Mosiah-Beal/411-Practicum/Planning Documents/Level1_Diagram.drawio.png

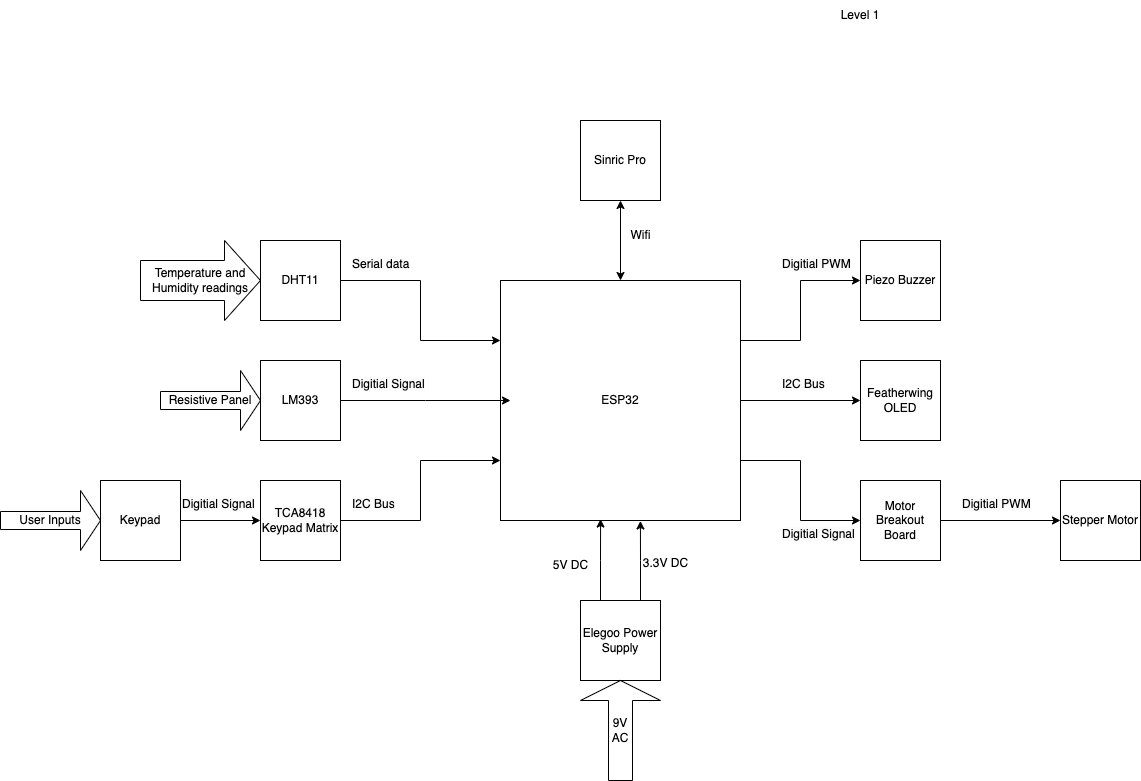
Planning Documents/Level1_Diagram.drawio.png
