Mosiah-Beal/411-Practicum/PNG's and PDF's/Planning Diagrams/411 Practicum Project Planning.drawio.pdf

# MAIN PR Undec

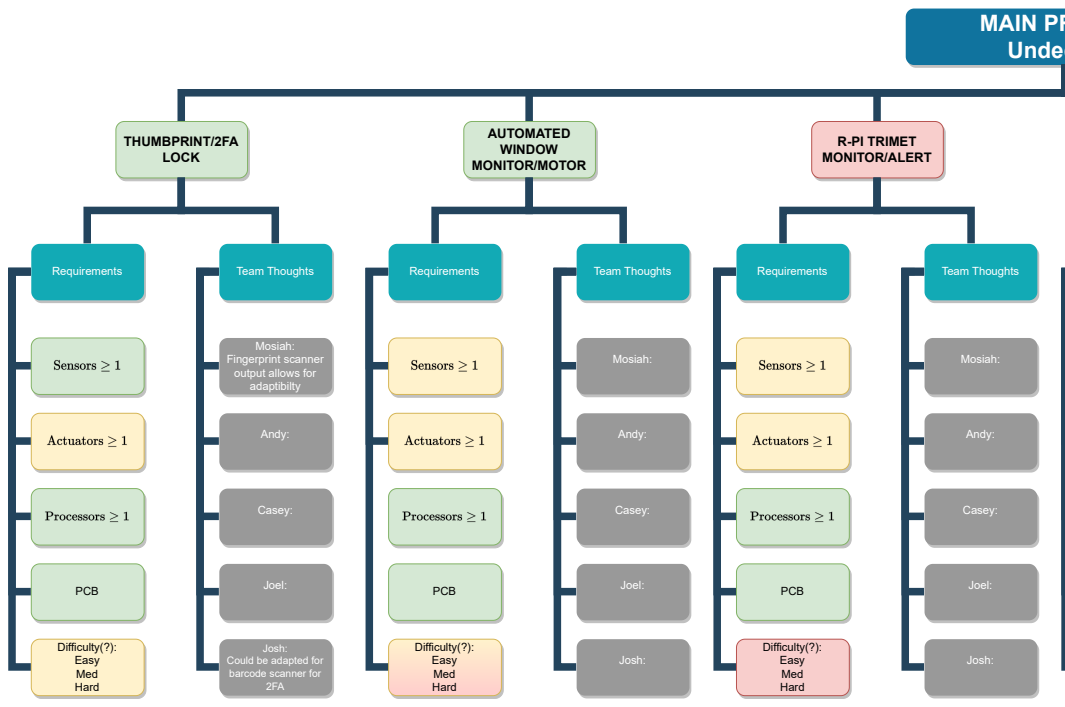
[picture p22: page 1]
THUMBPRINT/2FA LOCK; AUTOMATED WINDOW MONITOR/MOTOR; R-PI TRIMET MONITOR/ALERT; Requirements; Team Thoughts; PCB; Difficulty(?): Easy Med Hard; Andy:; Casey:; Joel:; Josh:; Difficulty(?): Easy Med; Mosiah:

Mosiah:
Fingerprint scanner
output allows for
adaptibilty

Could be adapted for
barcode scanner for

# ROJECT cided

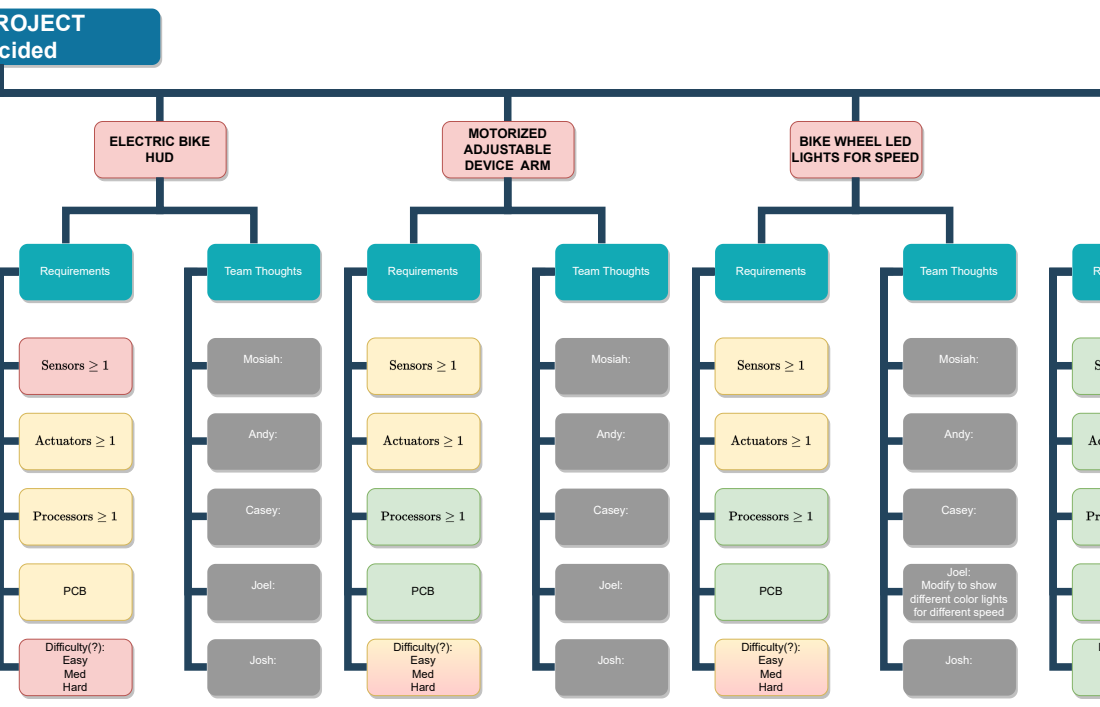
[picture p23: page 2]
ELECTRIC BIKE HUD; MOTORIZED ADJUSTABLE DEVICE ARM; Requirements; Team Thoughts; PCB; Difficulty(?): Easy Med; Mosiah:; Andy:; Casey:; Joel:; Josh:

BIKE WHEEL LED
LIGHTS FOR SPEED

Joel:
Modify to show
different color lights
for different speed

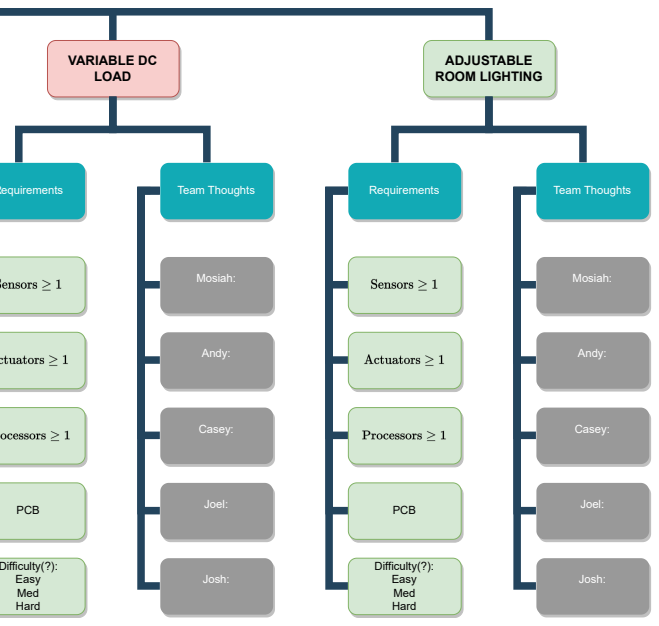
[picture p24: page 3]
VARIABLE DC LOAD; Requirements; Team Thoughts; PCB; Difficulty(?): Easy Med; Mosiah:; Andy:; Casey:; Joel:; Josh:; ADJUSTABLE ROOM LIGHTING
