Mosiah-Beal/411-Practicum/PNG's and PDF's/Schematics and PCBs/Archive/Window_Weather_Monitor-SCH_PCB_rev4.pdf

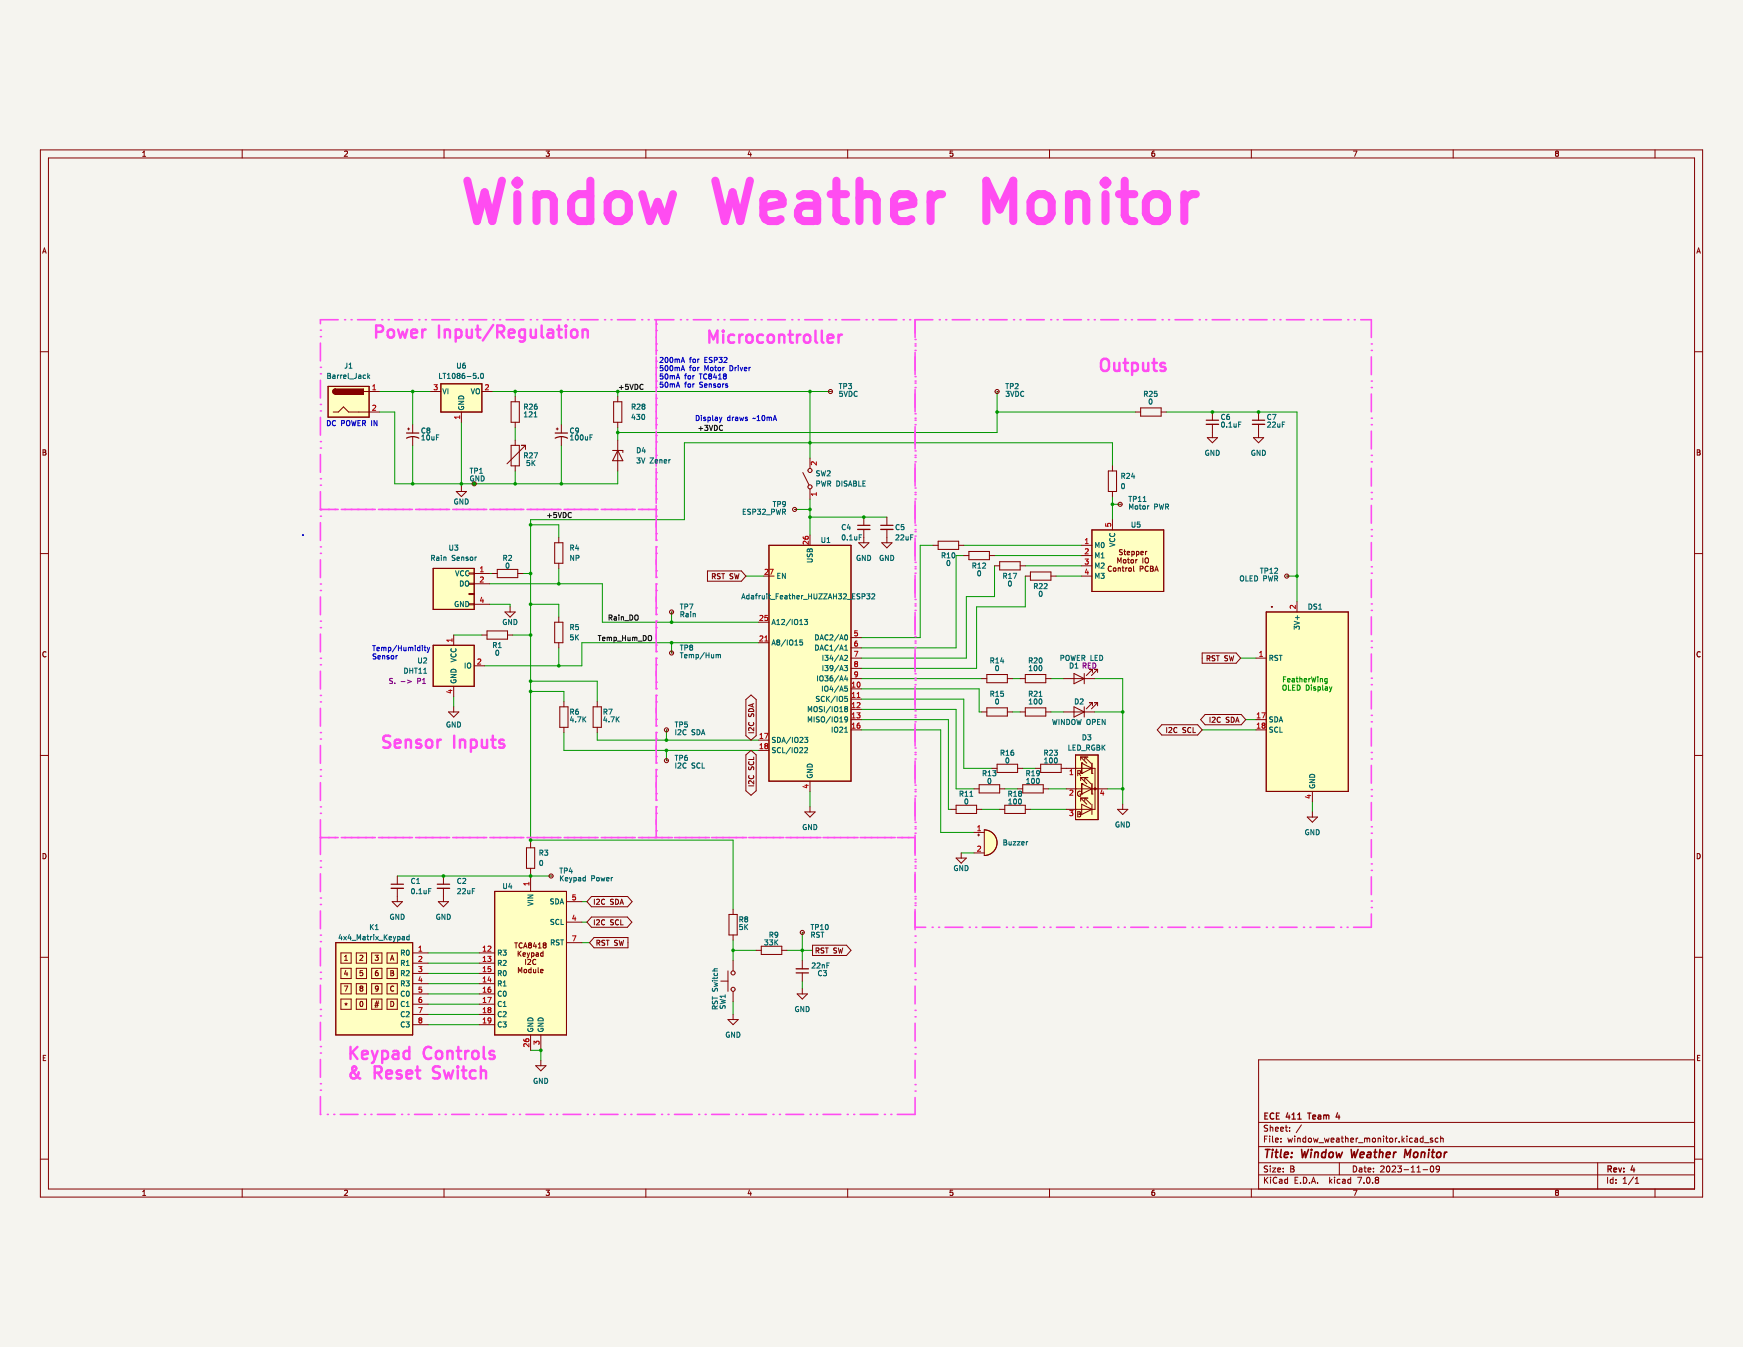
[picture p32: page 1]

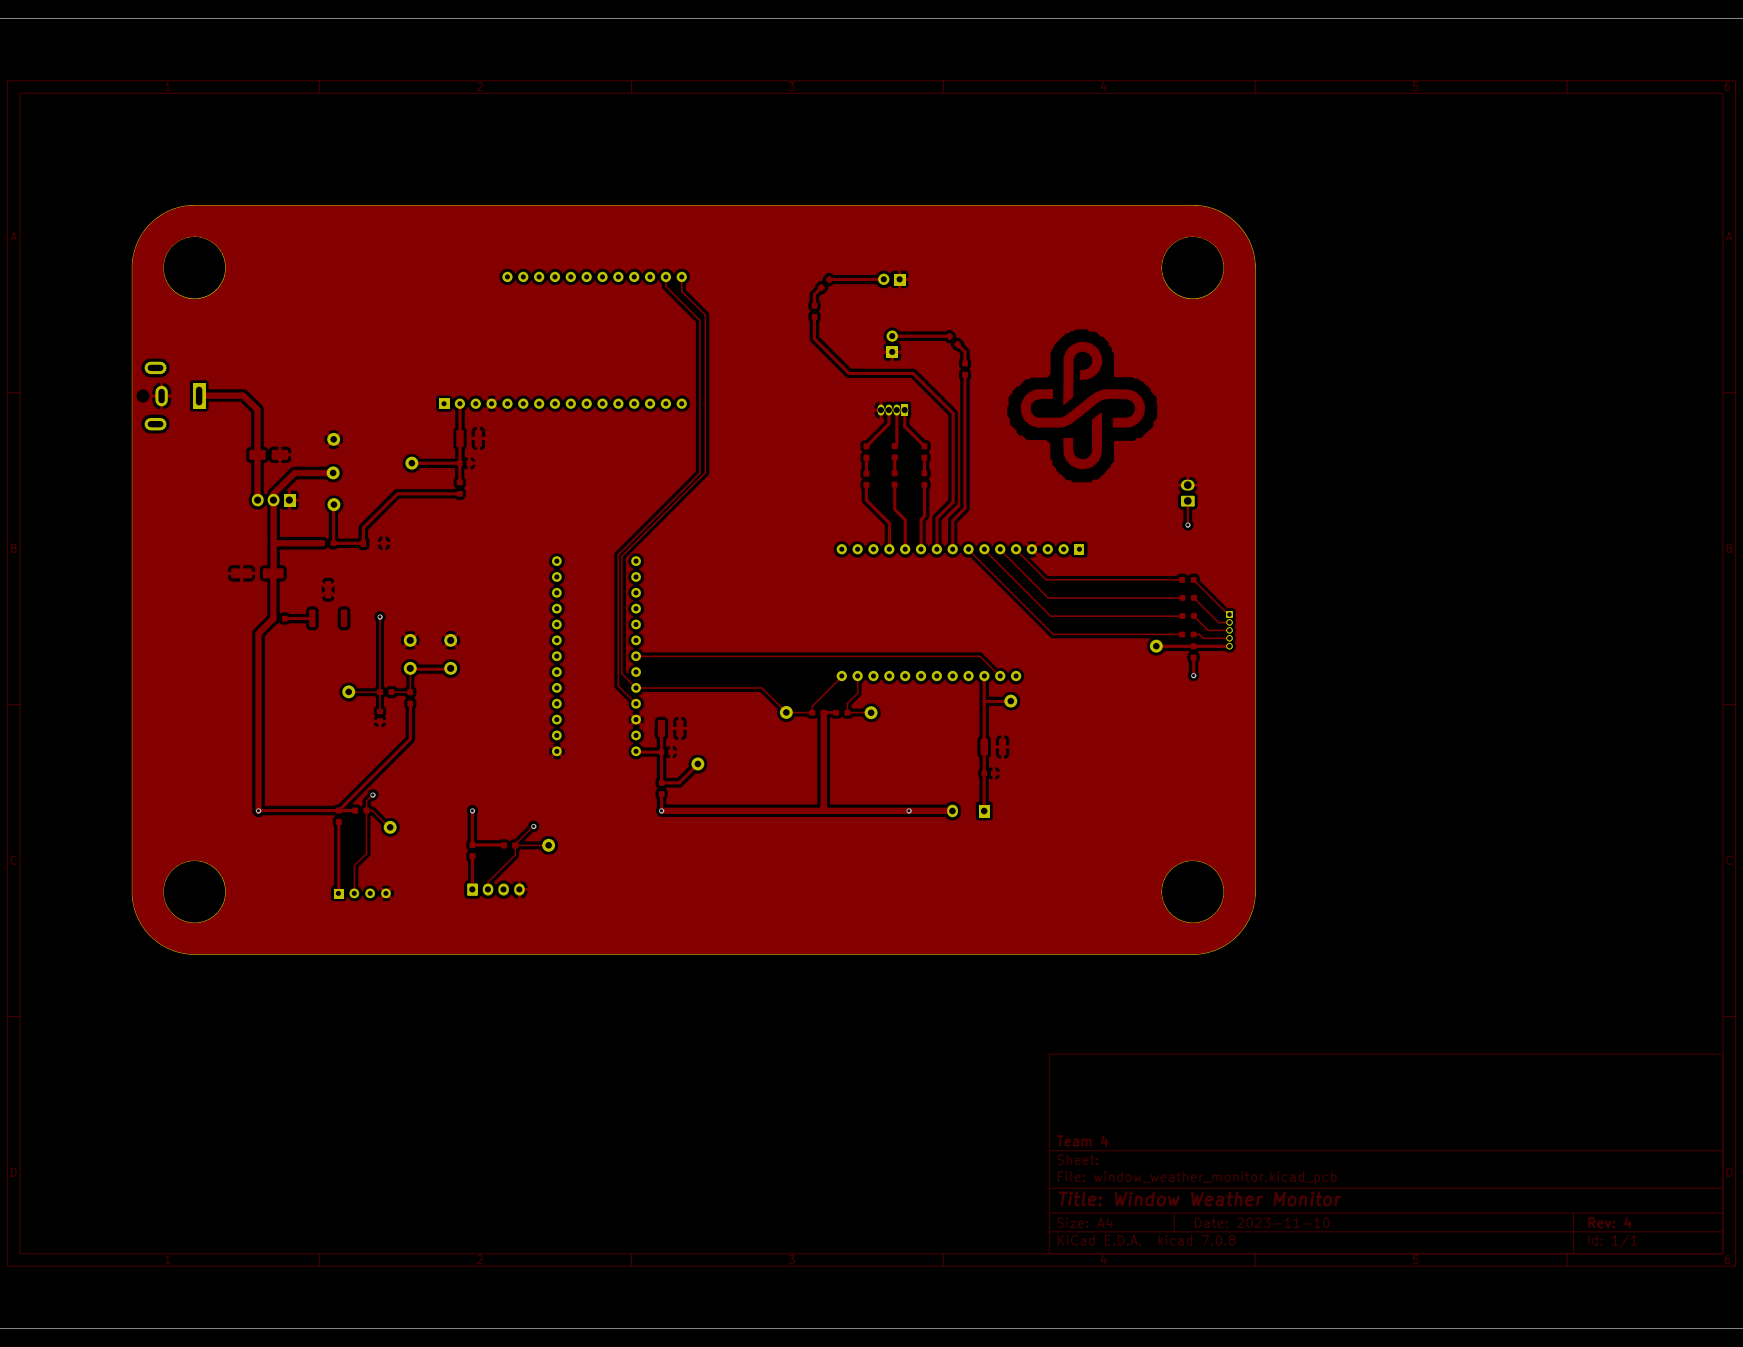
[picture p33: page 2]

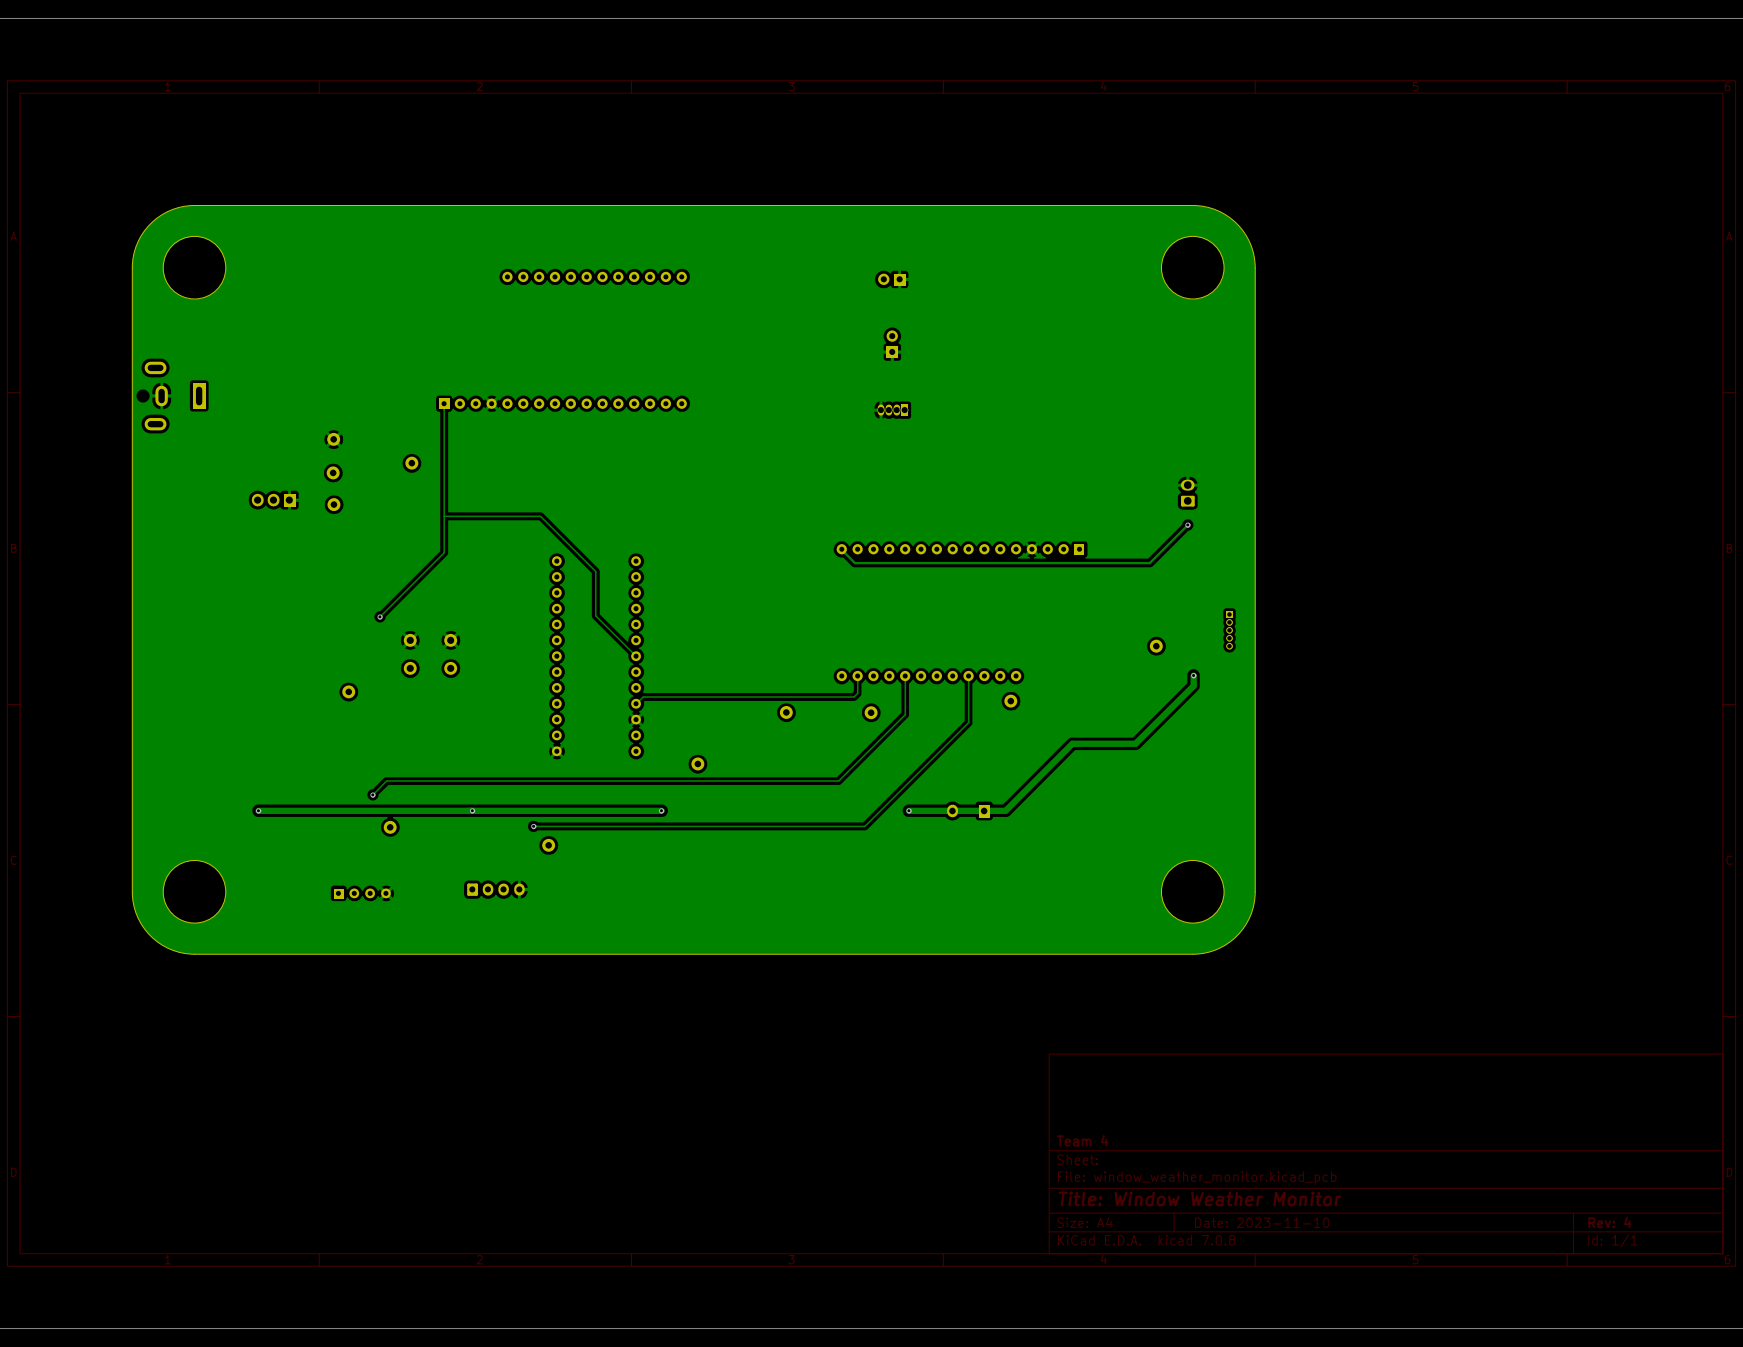
[picture p34: page 3]


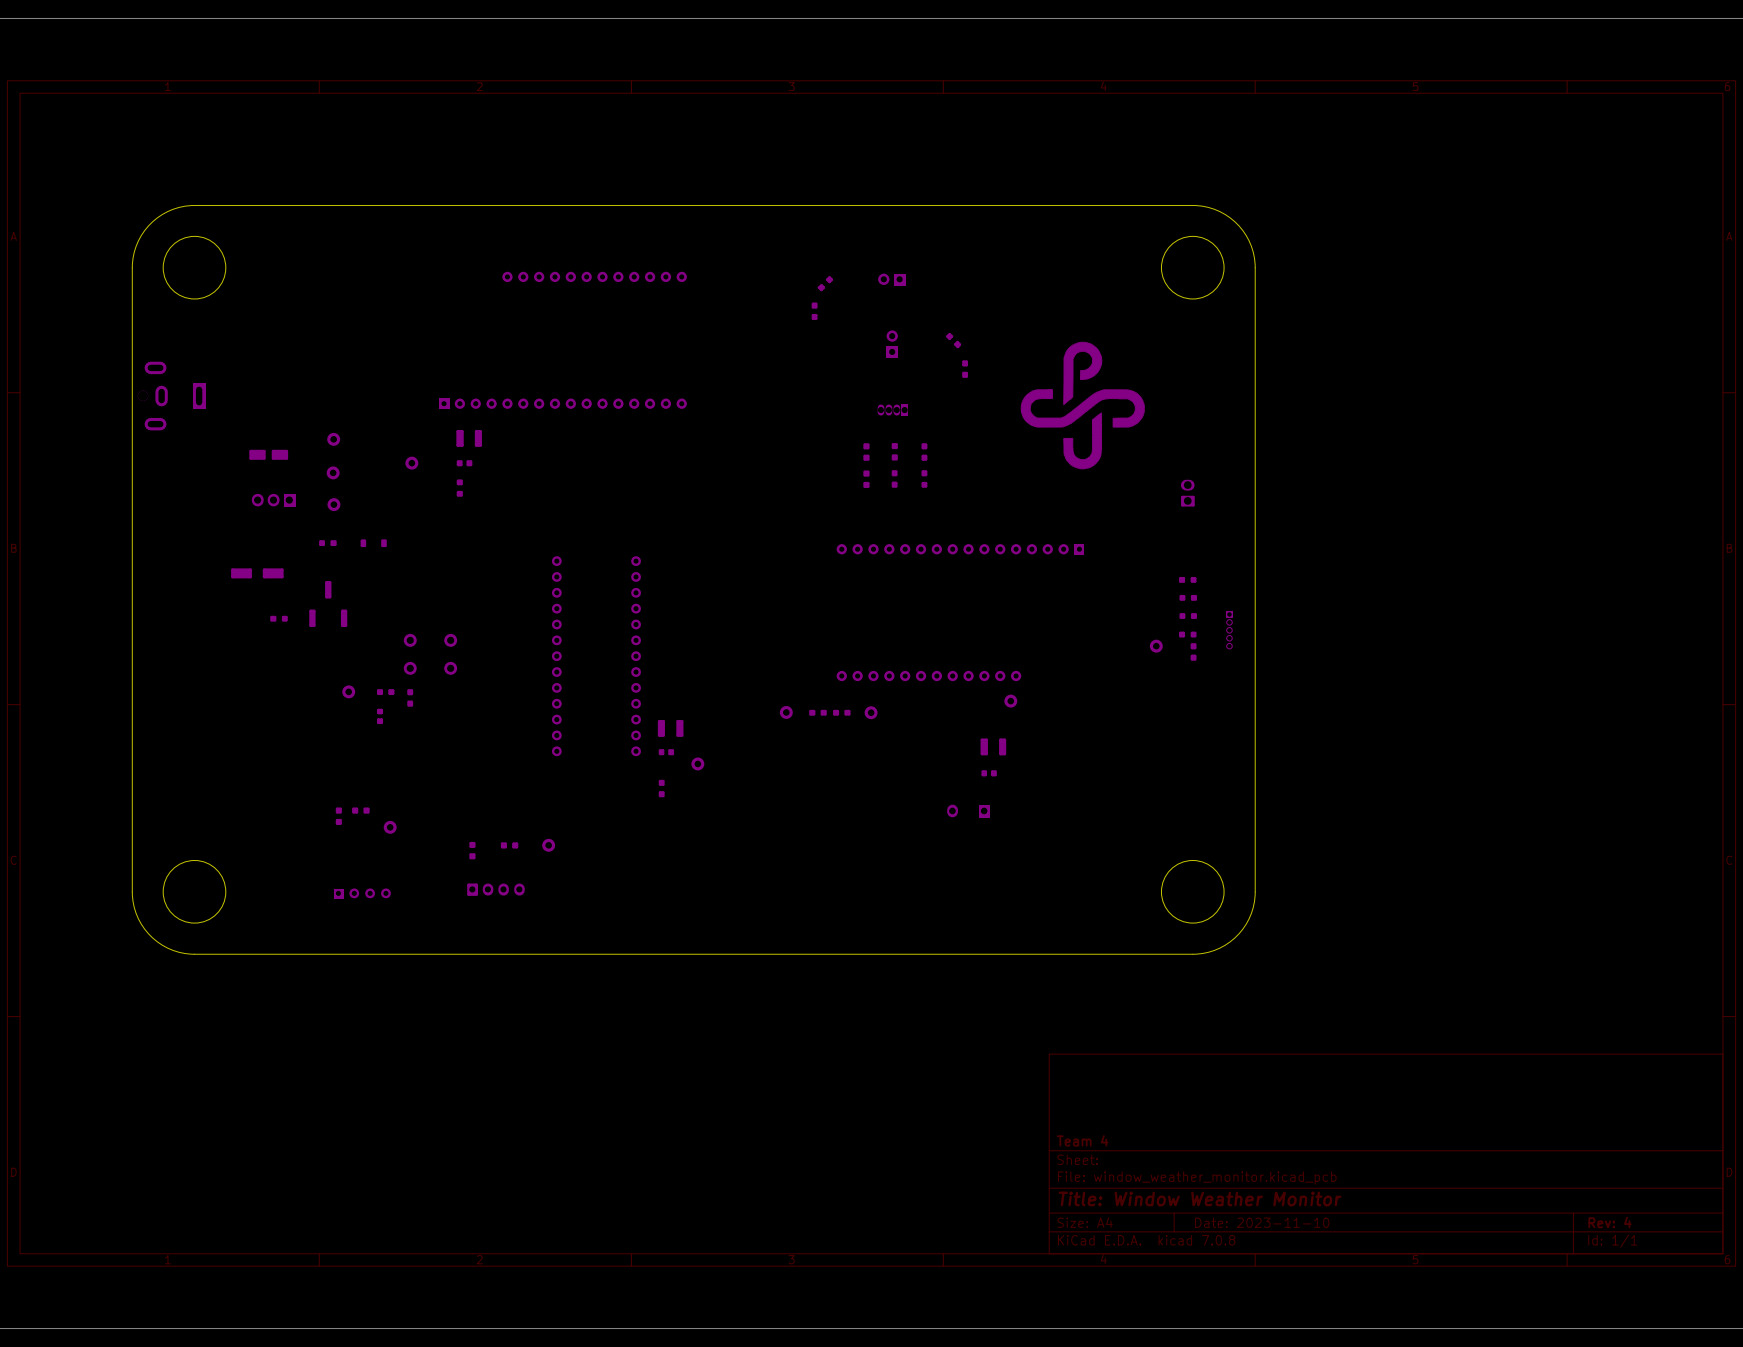
[picture p35: page 5]
