Mosiah-Beal/411-Practicum/PNG's and PDF's/Schematics and PCBs/Archive/Window_Weather_Monitor-PCB_rev3.pdf

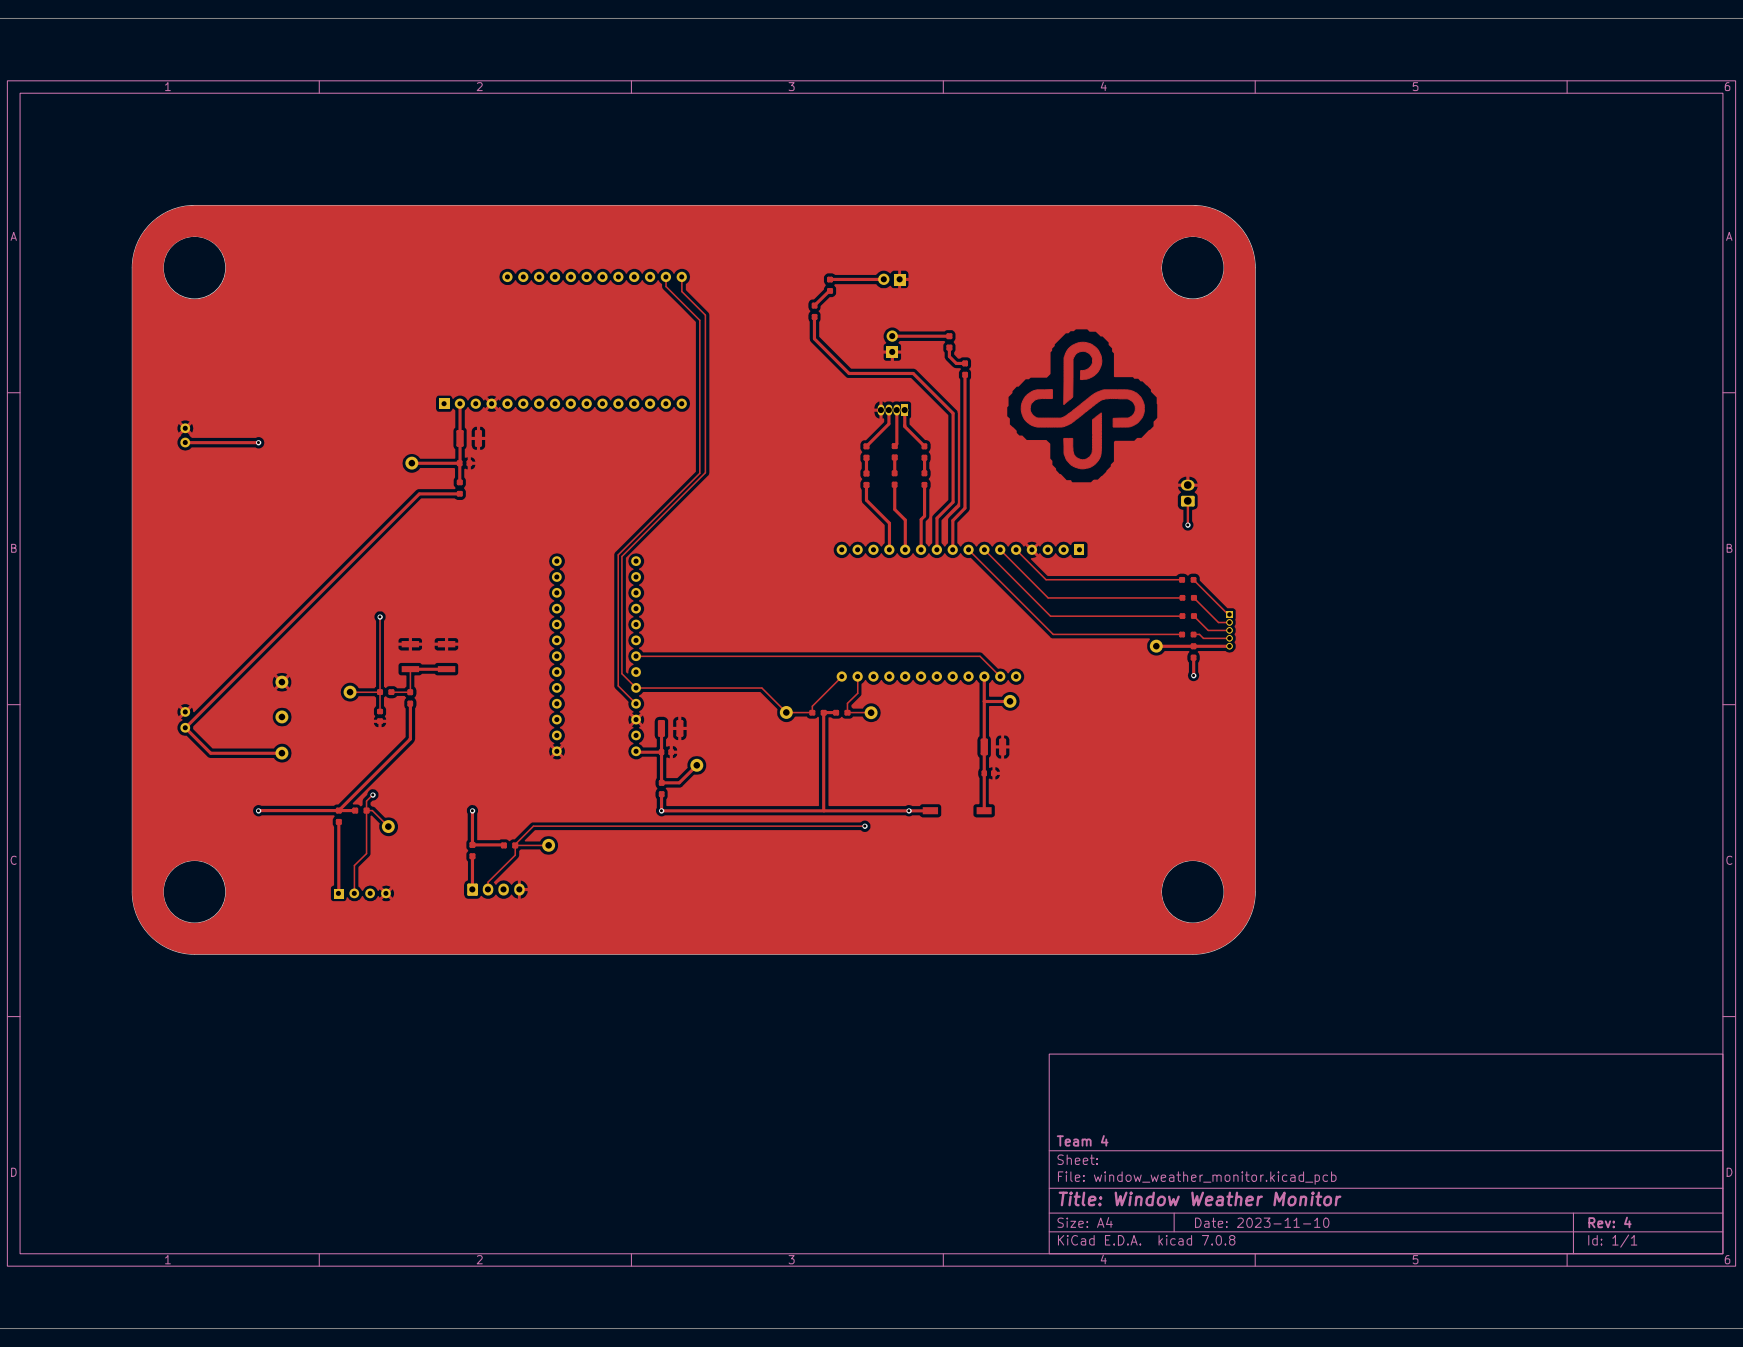
[picture p36: page 1]

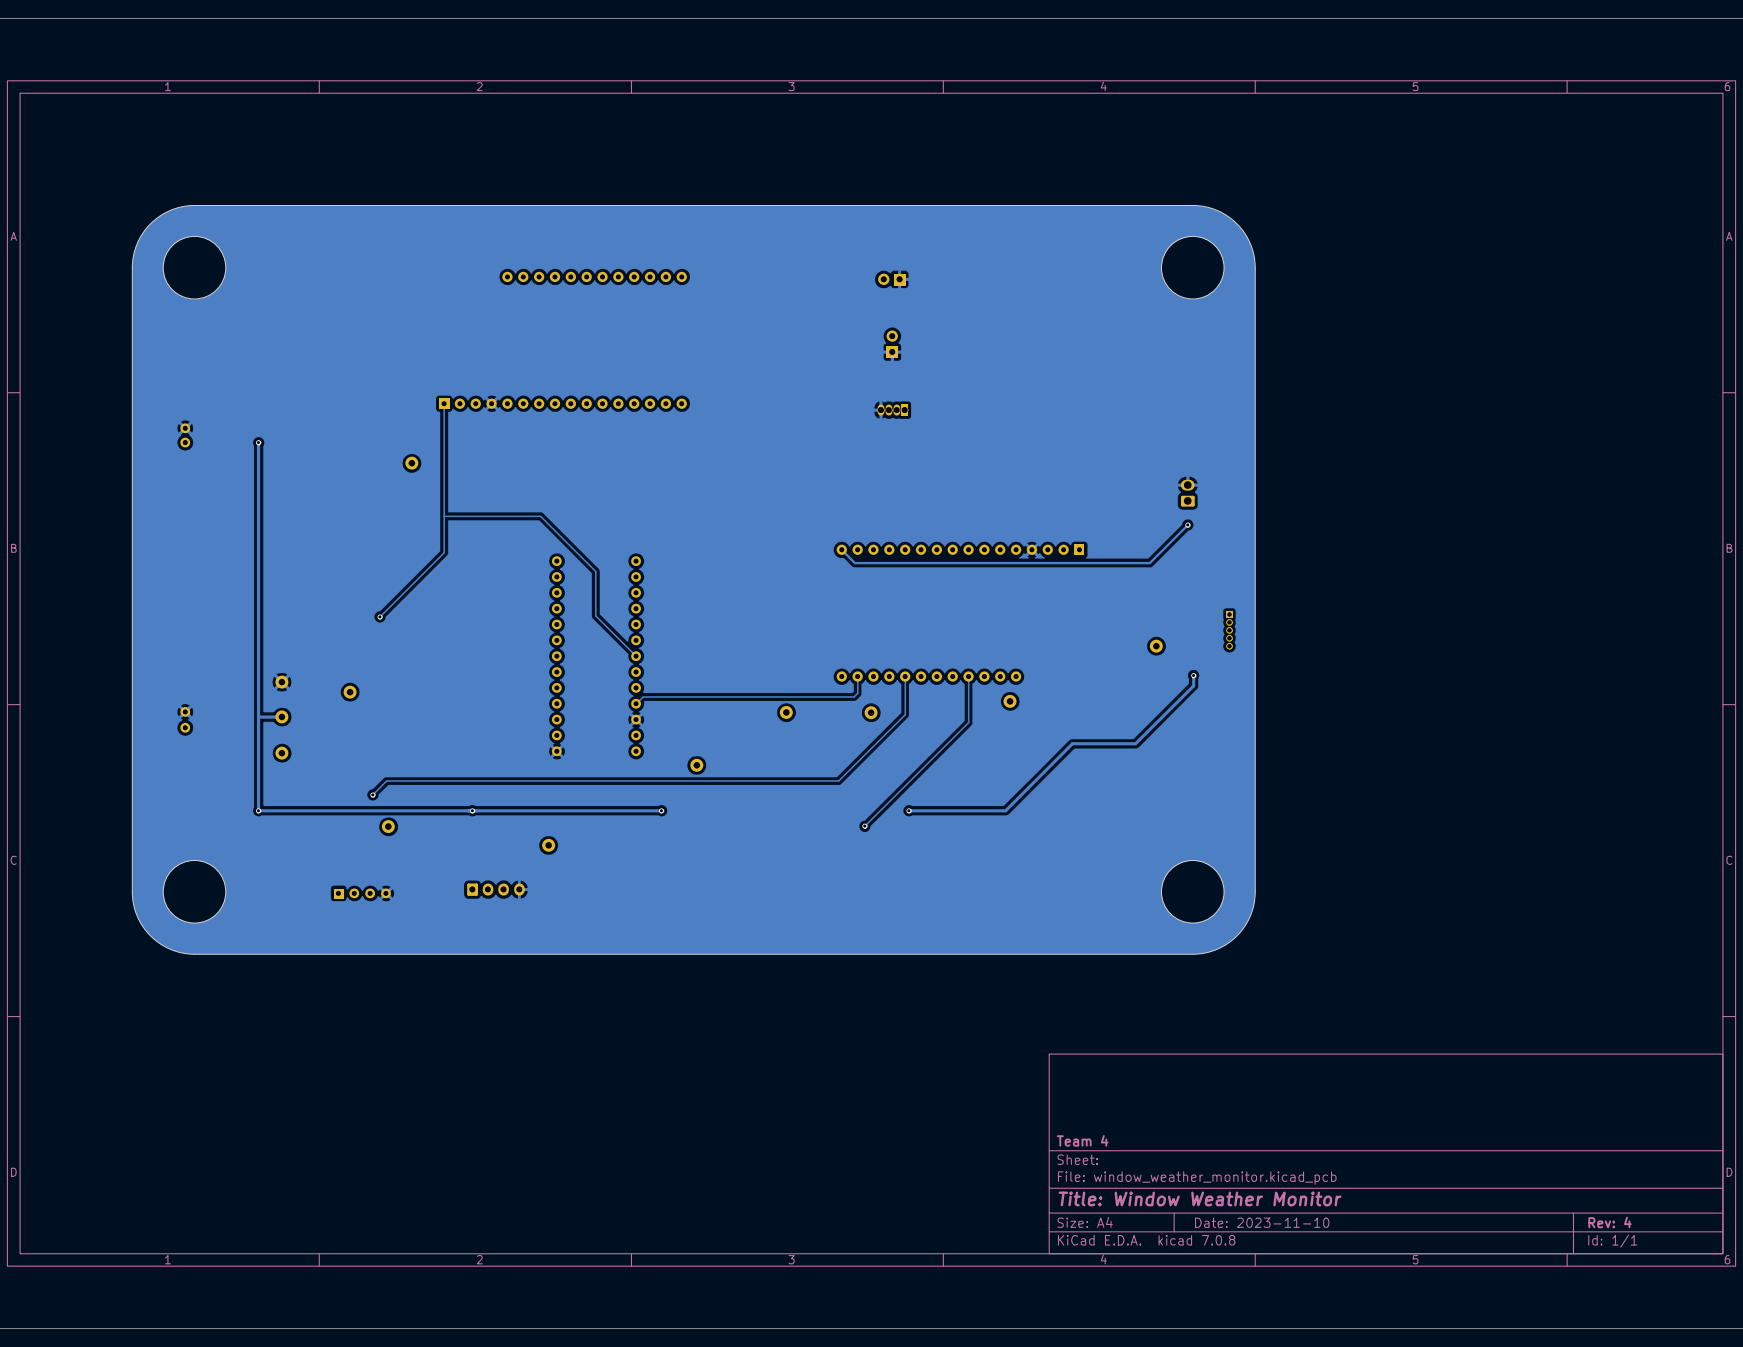
[picture p37: page 2]

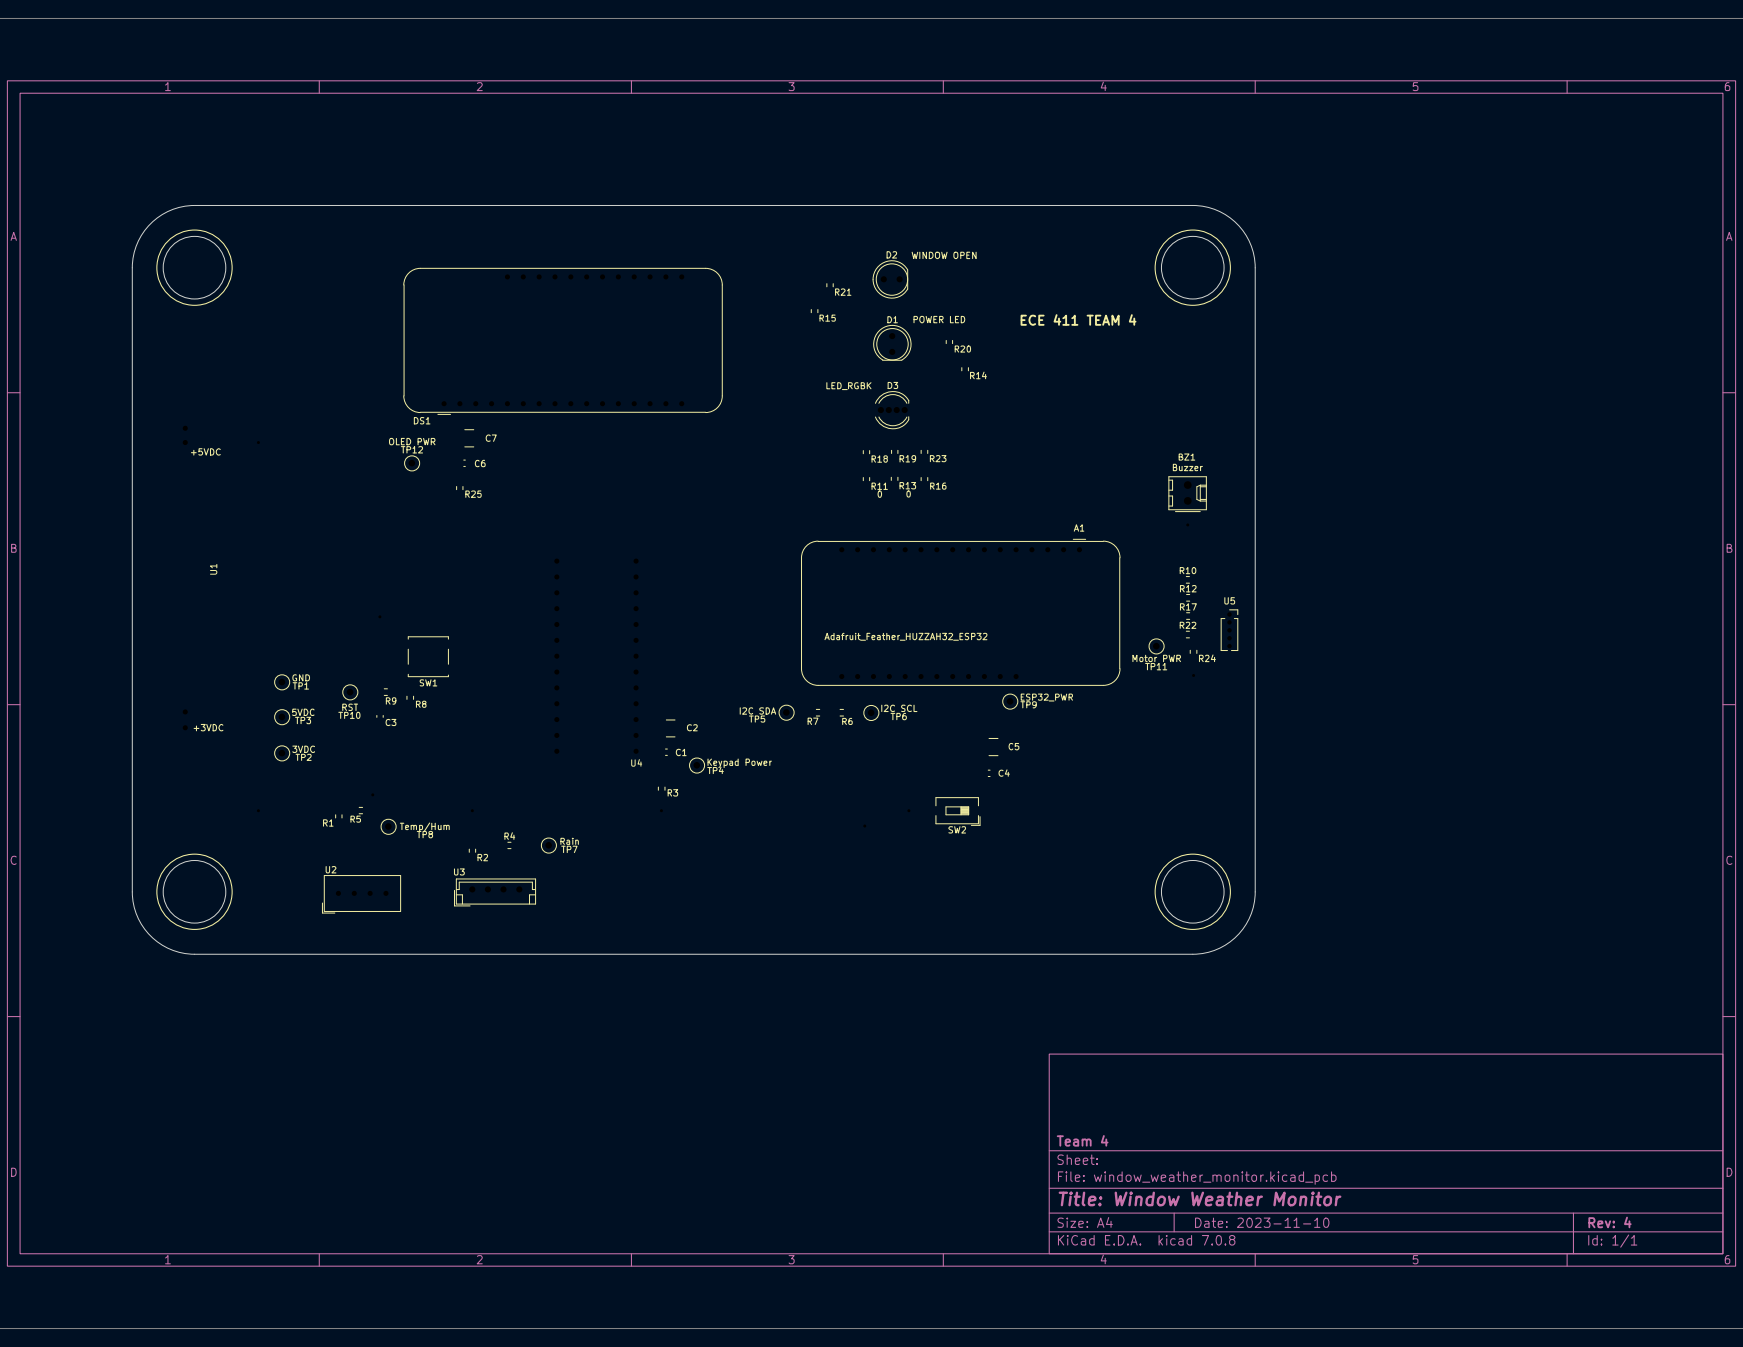
[picture p38: page 3]

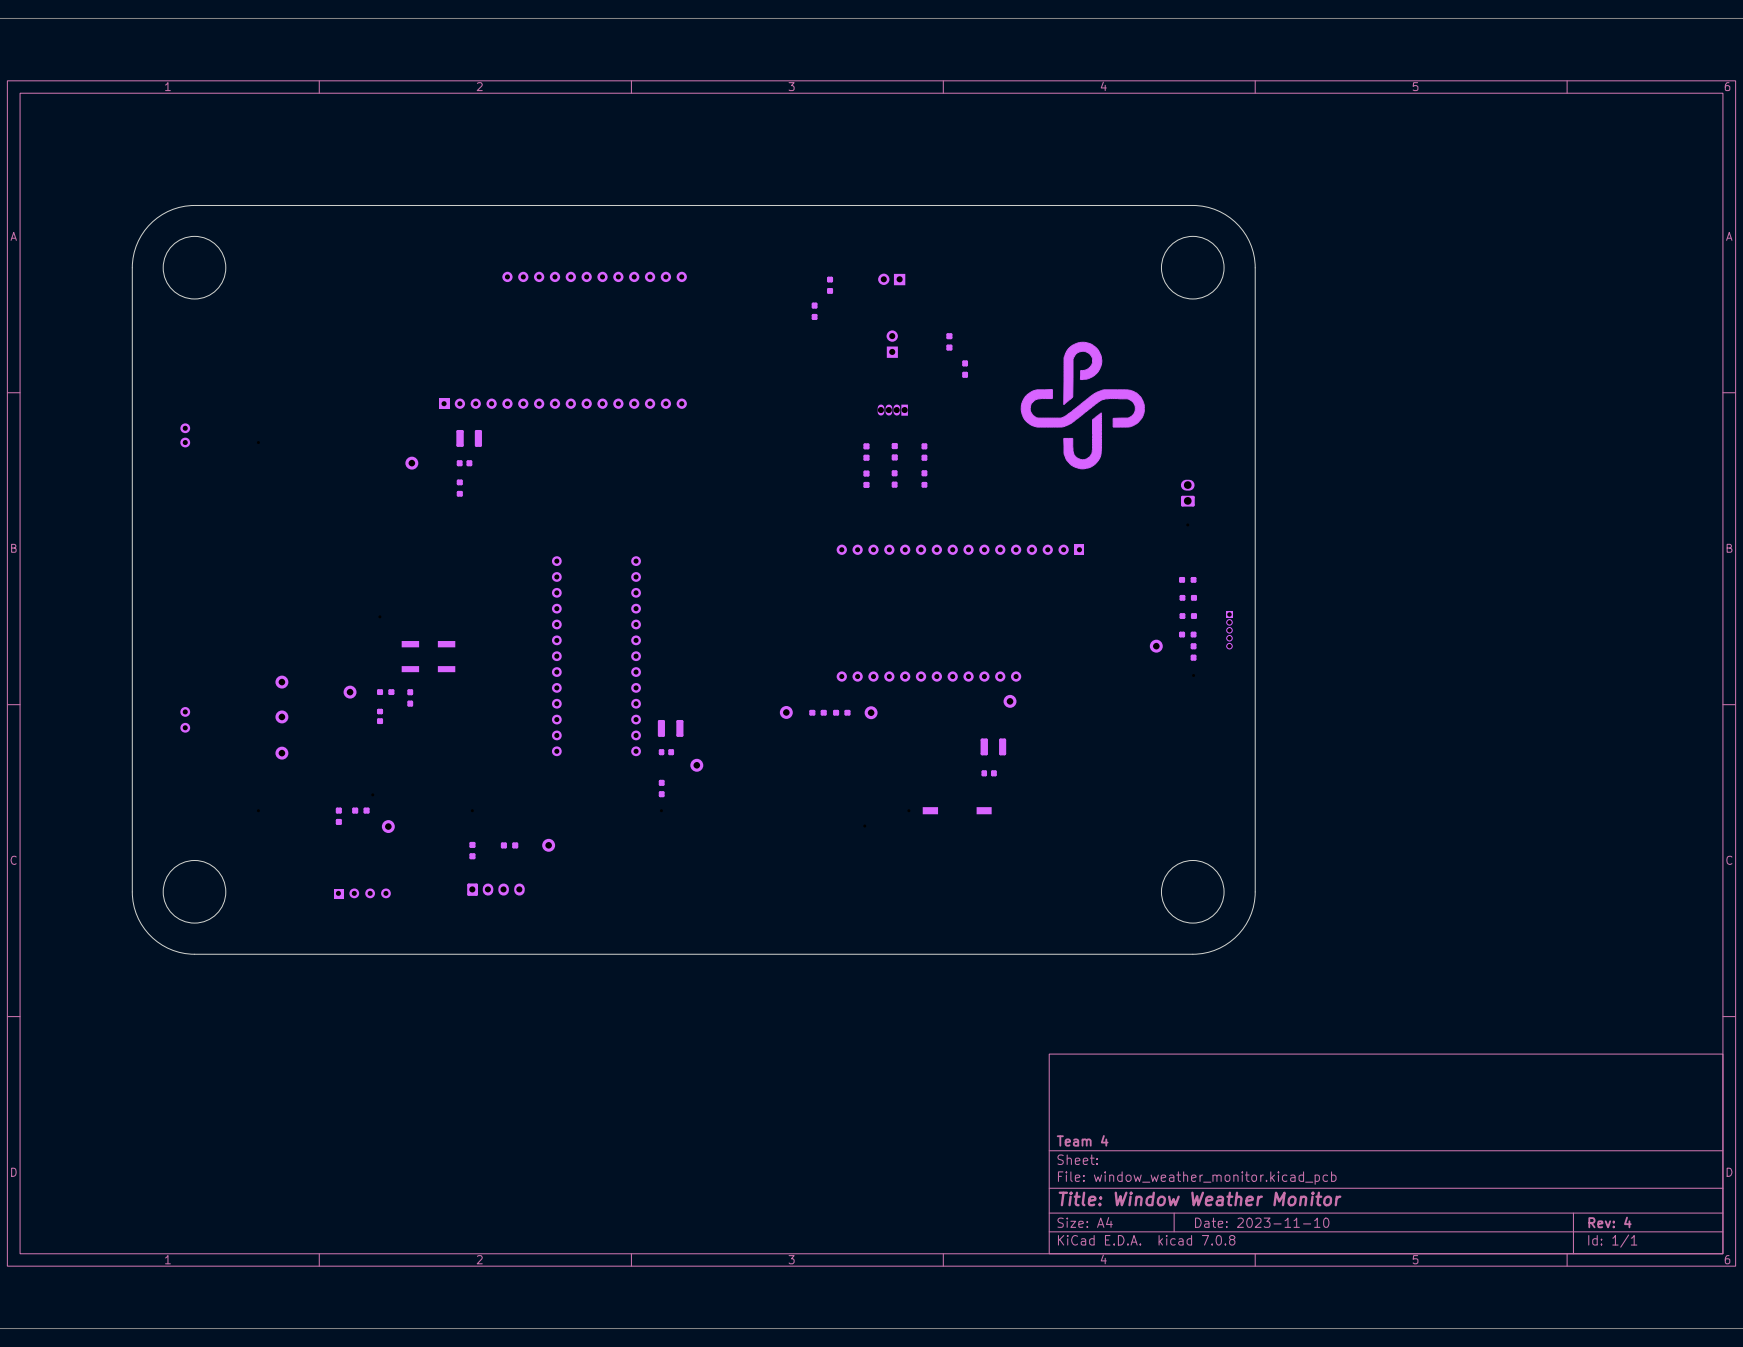
[picture p39: page 4]

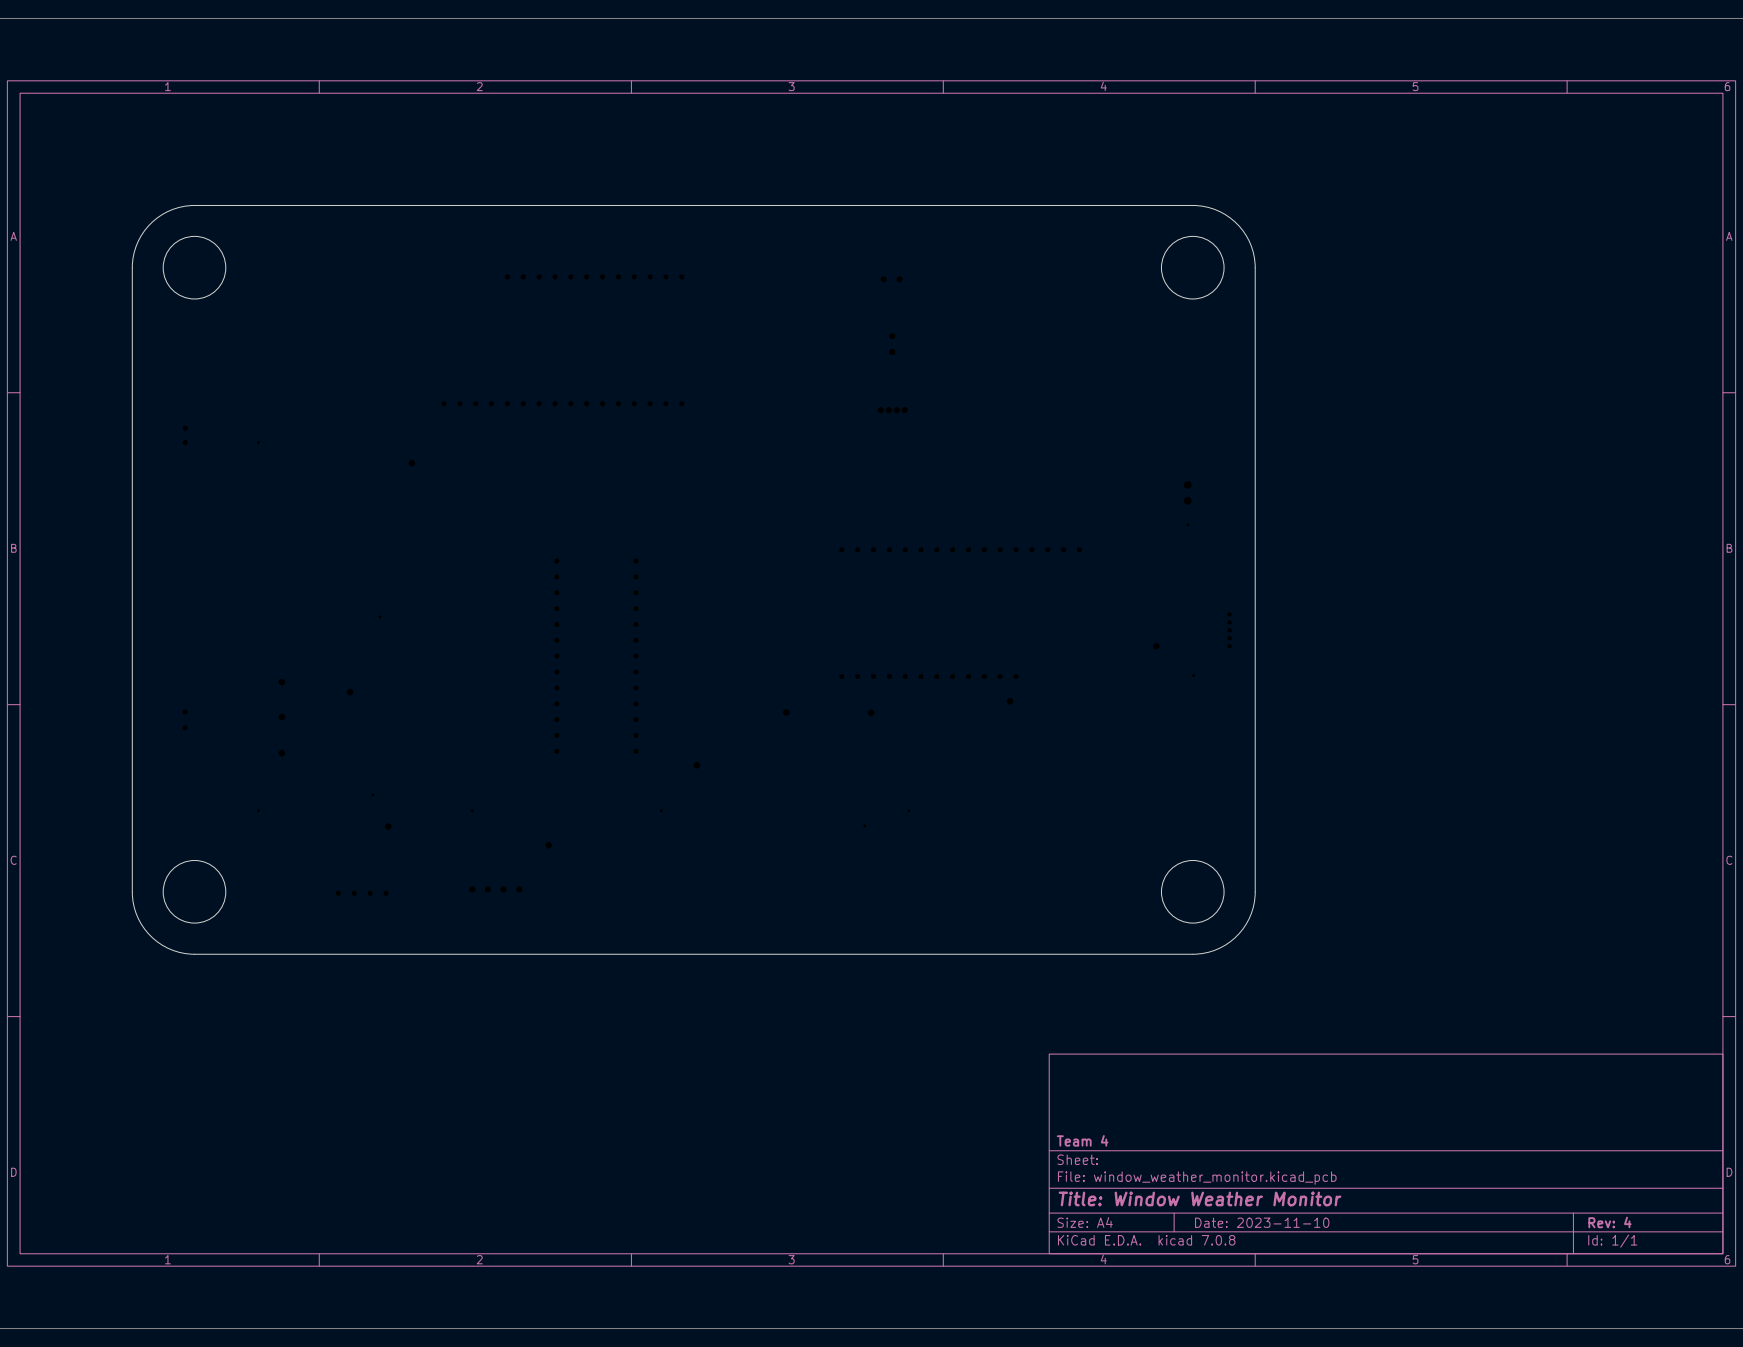
[picture p40: page 5]
