Mosiah-Beal/411-Practicum/PNG's and PDF's/Schematics and PCBs/Archive/Window_Weather_Monitor-SCH_PCB_rev3.pdf

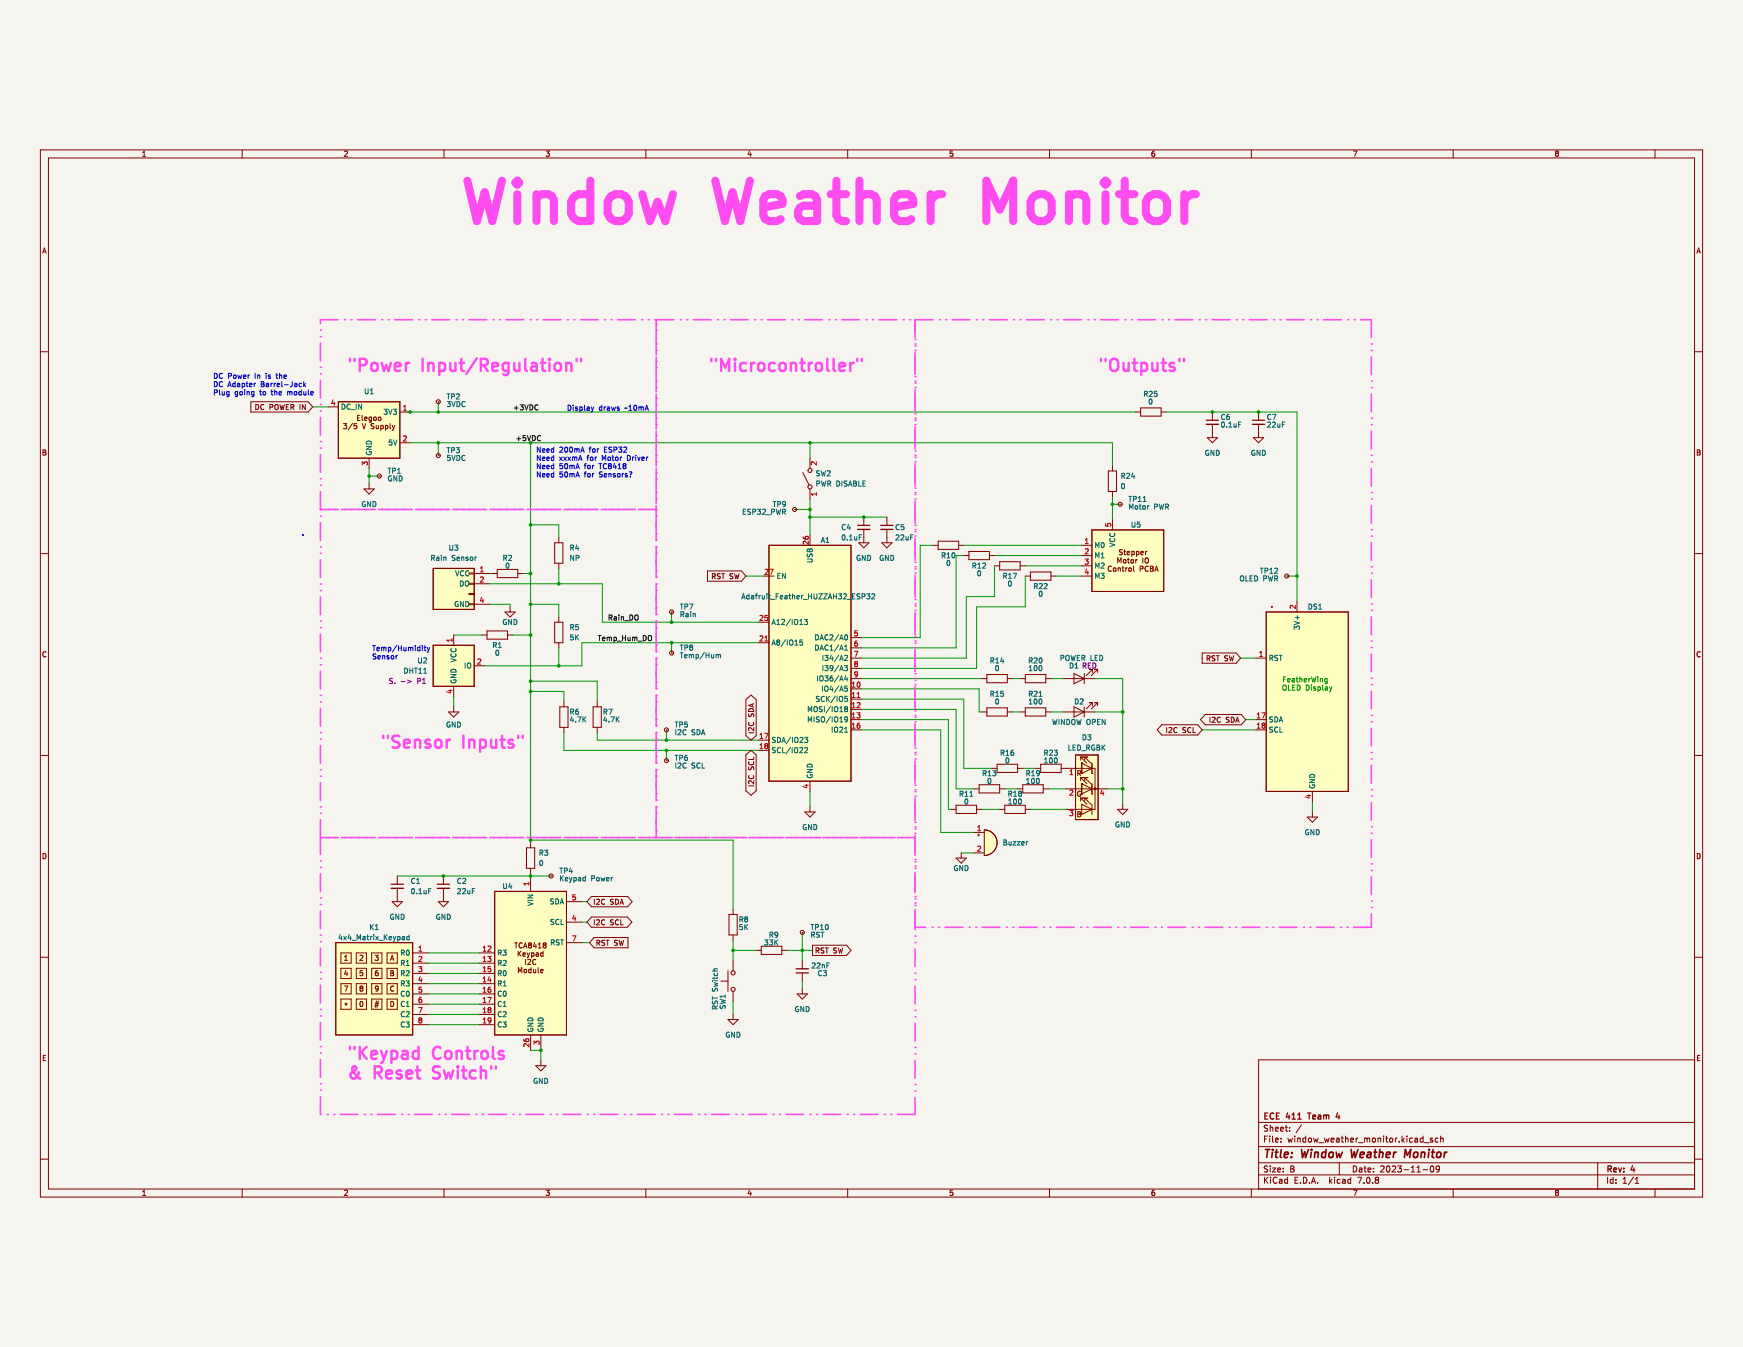
[picture p41: page 1]
