Mosiah-Beal/411-Practicum/PNG's and PDF's/Schematics and PCBs/Archive/Window_Weather_Monitor-PCB_rev2.pdf

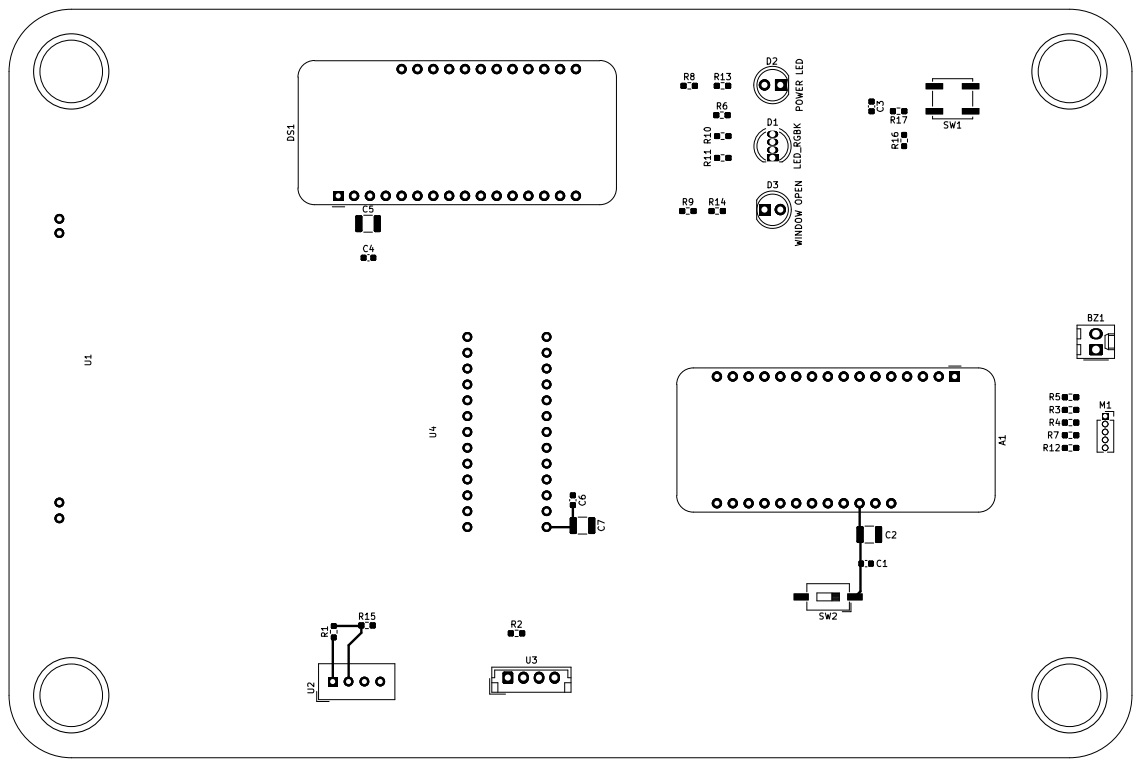
[picture p42: page 1]
